HaicoL/line-following-robot/images/CAR_PCB1.jpg

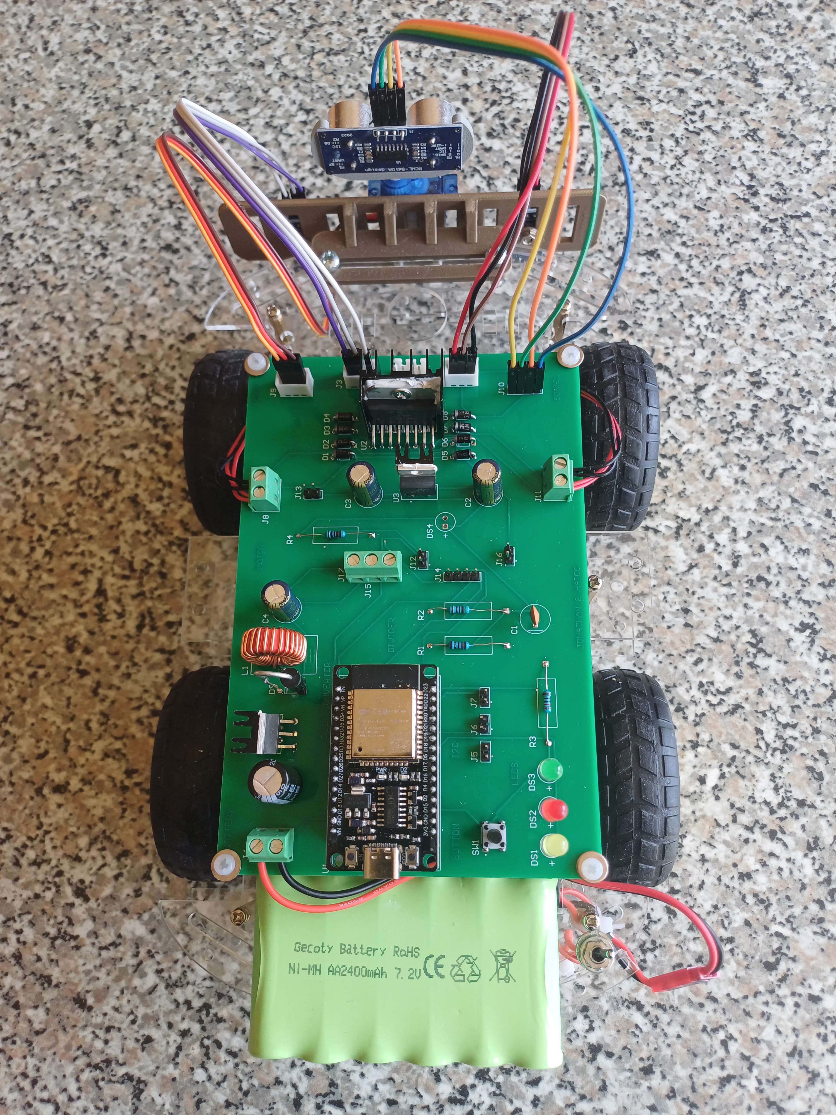
images/CAR_PCB1.jpg
